kalakris/kb_keycaps_chicago_stenographer/stl/single_keys/cs_r2_125.stl

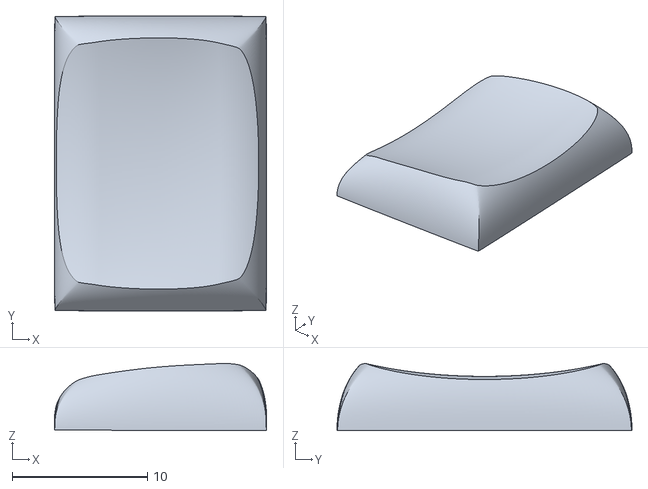
[picture p12: CAD file, 2026-03-17]
stl/single_keys/cs_r2_125.stl
15.7 x 21.8 x 4.95
