kalakris/kb_keycaps_chicago_stenographer/view_stl.scad

// Quick STL viewer - override stl_file and view params via -D
stl_file = "stl/debug/trap_t2_convex.stl";
import(stl_file);
