kalakris/kb_keycaps_chicago_stenographer/test_trap.scad

use <Choc_Chicago_Steno_Thumb_Trap.scad>
test_keyID = 0;
test_dish = "convex";
keycap_cs_thumb_trap(keyID=test_keyID, dishType=test_dish, Stem=true, StemRot=0, Dish=true);
